hardwario/twr-enclosures/doc/bce202-1.png

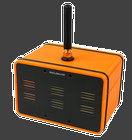
doc/bce202-1.png
