hardwario/twr-enclosures/doc/bce202-2.png

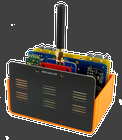
doc/bce202-2.png
