hardwario/twr-enclosures/doc/bce204-1.png

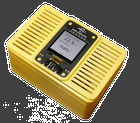
doc/bce204-1.png
