hardwario/twr-enclosures/doc/bce501-1.png

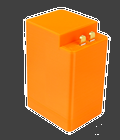
doc/bce501-1.png
