hardwario/twr-enclosures/stl-models/HWE105B.stl

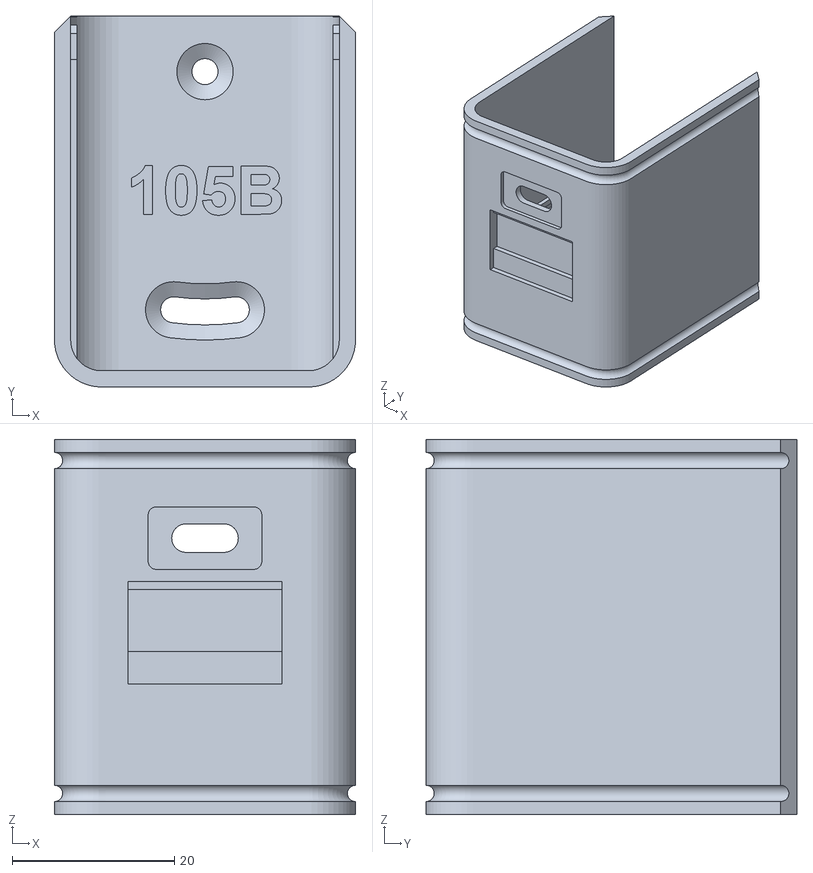
[picture p47: CAD file, 2020-03-29]
stl-models/HWE105B.stl
37.1 x 45.7 x 46.2
