hardwario/twr-enclosures/stl-models/HWE501B.stl

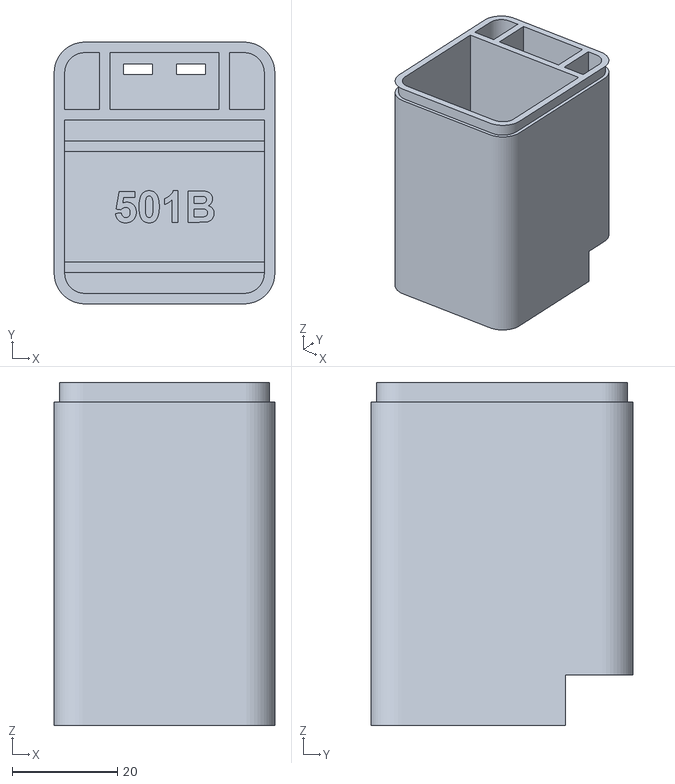
[picture p48: CAD file, 2020-03-29]
stl-models/HWE501B.stl
42.0 x 49.8 x 65.3
