hardwario/twr-enclosures/stl-models/HWE205A.stl

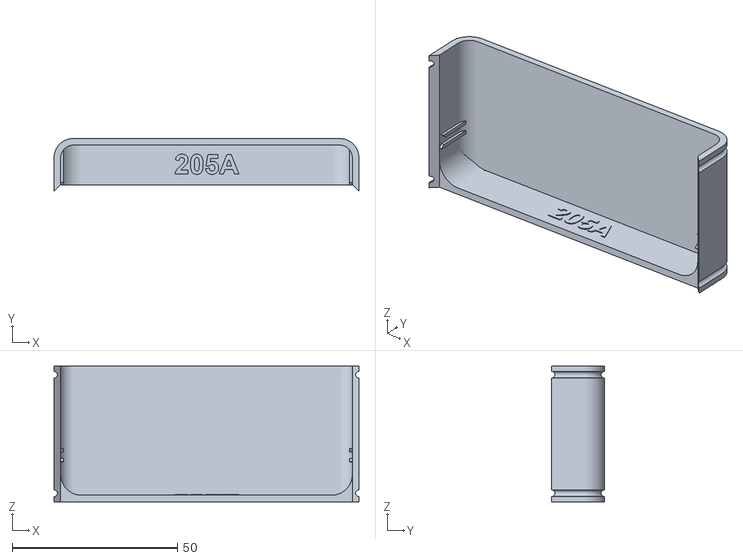
[picture p49: CAD file, 2020-03-29]
stl-models/HWE205A.stl
92.2 x 16.0 x 41.0
