hardwario/twr-enclosures/stl-models/HWE209C.stl

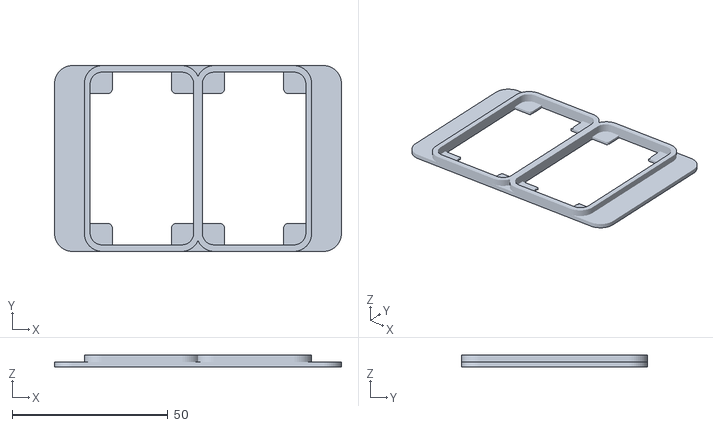
[picture p50: CAD file, 2020-03-29]
stl-models/HWE209C.stl
92.2 x 59.7 x 4.00
