hardwario/twr-enclosures/stl-models/HWE302A.stl

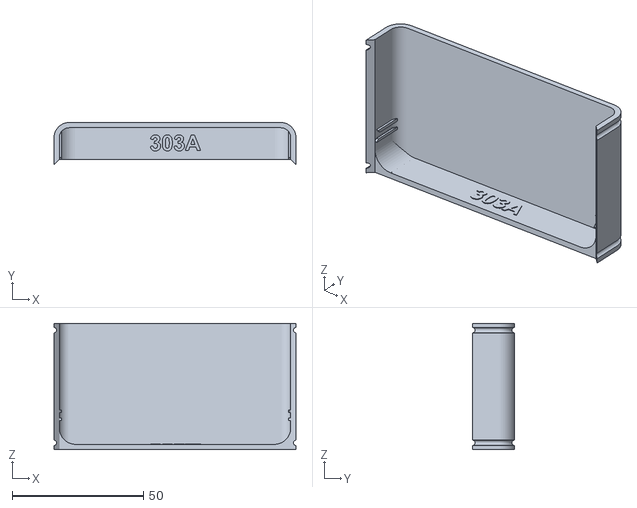
[picture p51: CAD file, 2020-03-29]
stl-models/HWE302A.stl
92.2 x 16.0 x 48.1
