hardwario/twr-enclosures/stl-models/HWE205B.stl

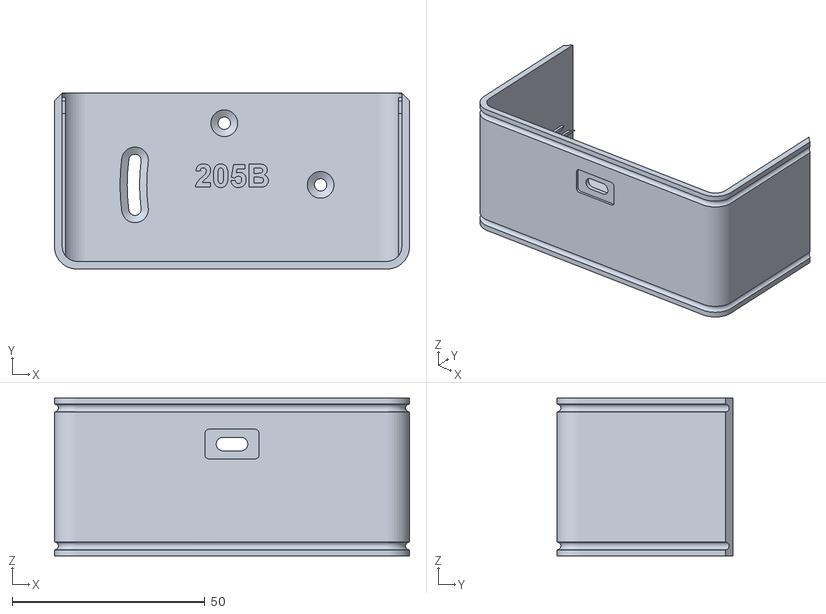
[picture p52: CAD file, 2020-03-29]
stl-models/HWE205B.stl
92.2 x 45.7 x 41.0
