hardwario/twr-enclosures/stl-models/HWE501A.stl

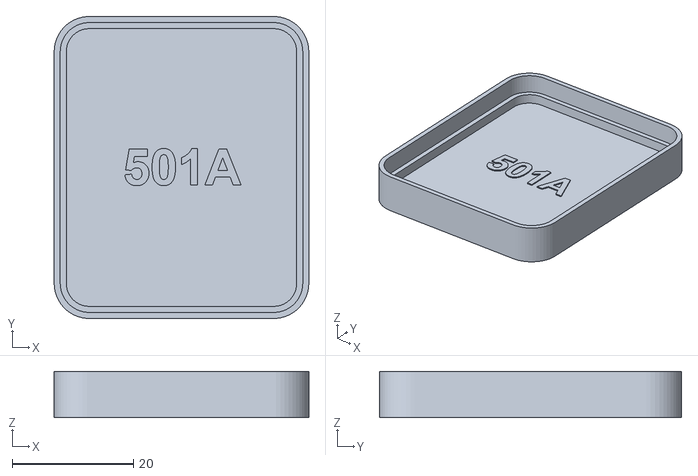
[picture p53: CAD file, 2020-03-29]
stl-models/HWE501A.stl
42.0 x 49.8 x 7.60
