hardwario/twr-enclosures/stl-models/HWE104B.stl

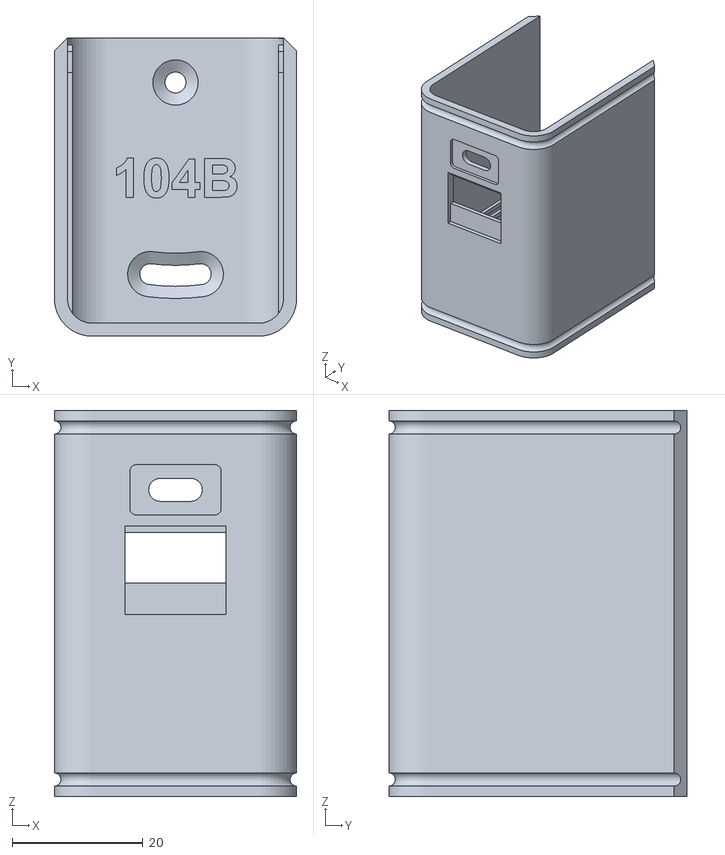
[picture p54: CAD file, 2020-03-29]
stl-models/HWE104B.stl
37.1 x 45.7 x 59.1
