hardwario/twr-enclosures/stl-models/HWE302C.stl

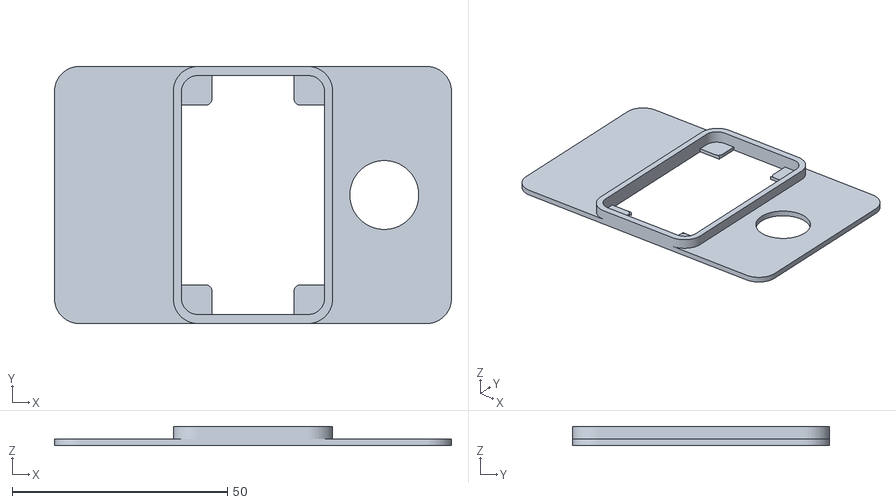
[picture p55: CAD file, 2020-03-29]
stl-models/HWE302C.stl
92.2 x 59.7 x 4.50
