hardwario/twr-enclosures/stl-models/HWE202A.stl

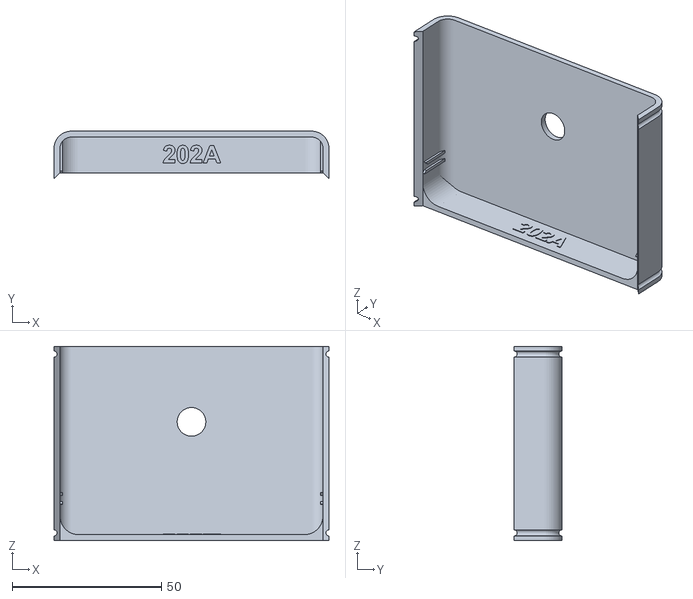
[picture p56: CAD file, 2020-03-29]
stl-models/HWE202A.stl
92.2 x 16.0 x 65.1
