hardwario/twr-enclosures/stl-models/HWE204B.stl

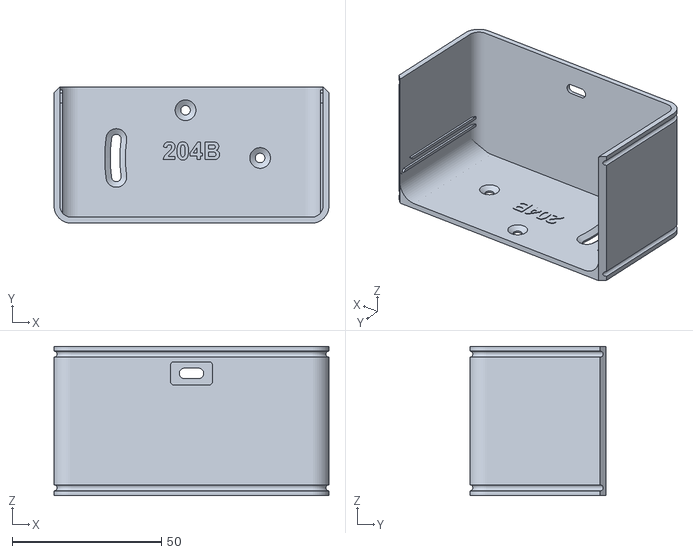
[picture p57: CAD file, 2020-03-29]
stl-models/HWE204B.stl
92.2 x 45.7 x 50.0
