hardwario/twr-enclosures/stl-models/HWE202B.stl

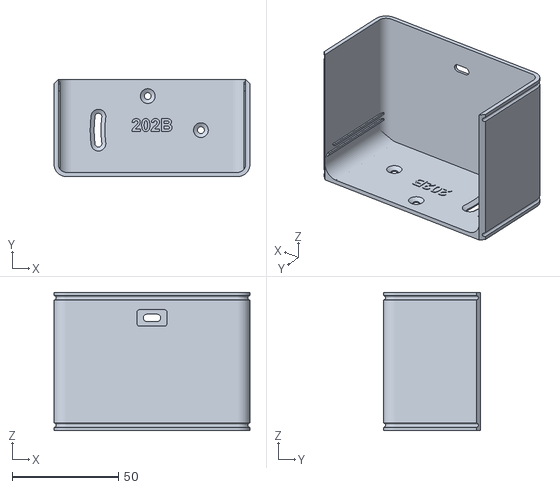
[picture p58: CAD file, 2020-03-29]
stl-models/HWE202B.stl
92.2 x 45.7 x 65.1
