hardwario/twr-enclosures/stl-models/HWE204C.stl

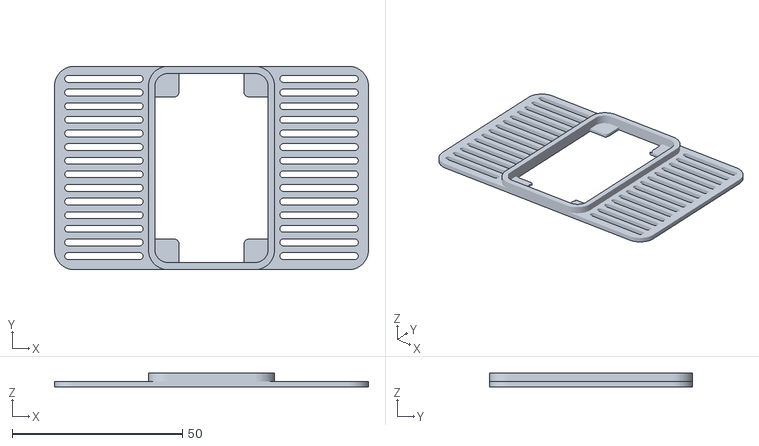
[picture p59: CAD file, 2020-03-29]
stl-models/HWE204C.stl
92.2 x 59.7 x 4.00
