hardwario/twr-enclosures/stl-models/HWE305A.stl

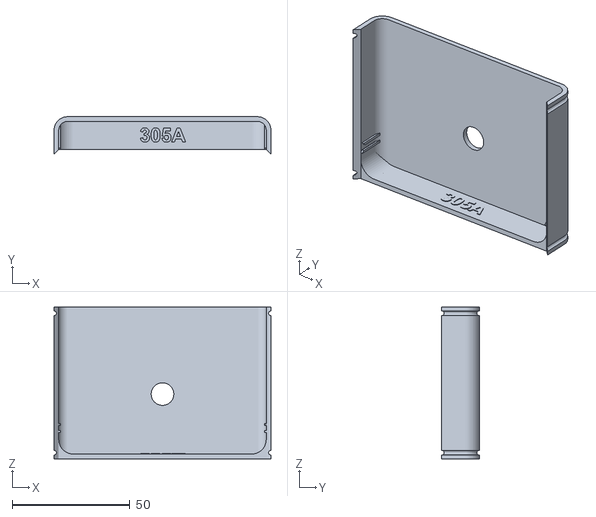
[picture p60: CAD file, 2020-03-29]
stl-models/HWE305A.stl
92.2 x 16.0 x 64.4
