hardwario/twr-enclosures/stl-models/HWE101B.stl

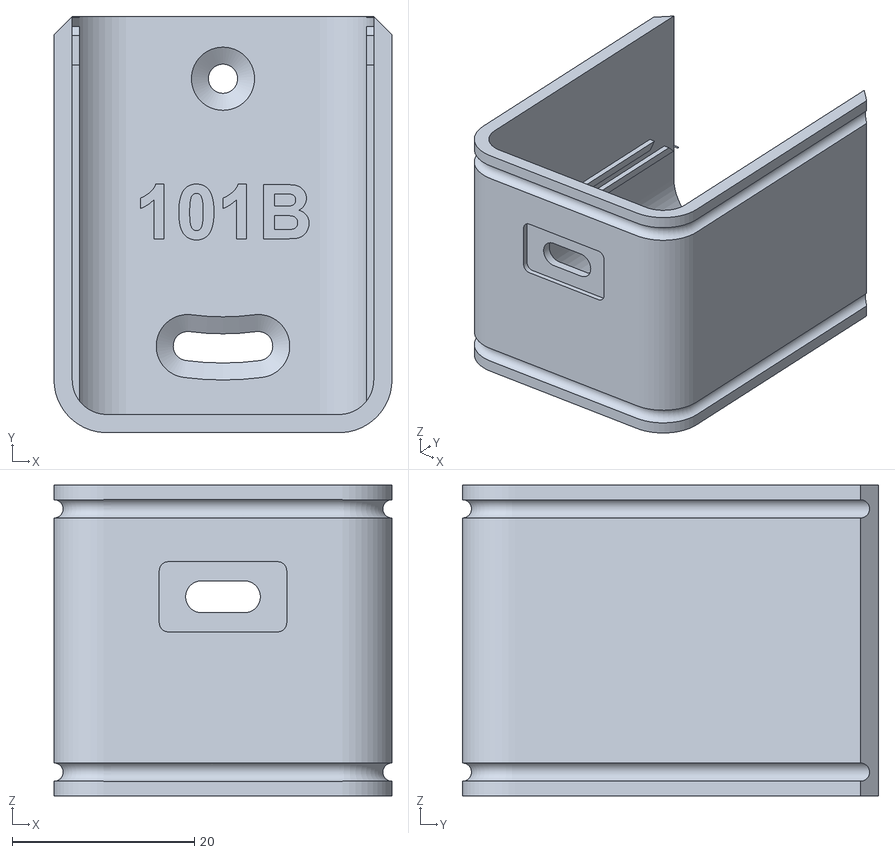
[picture p61: CAD file, 2020-03-29]
stl-models/HWE101B.stl
37.1 x 45.7 x 34.1
