hardwario/twr-enclosures/stl-models/HWE206A.stl

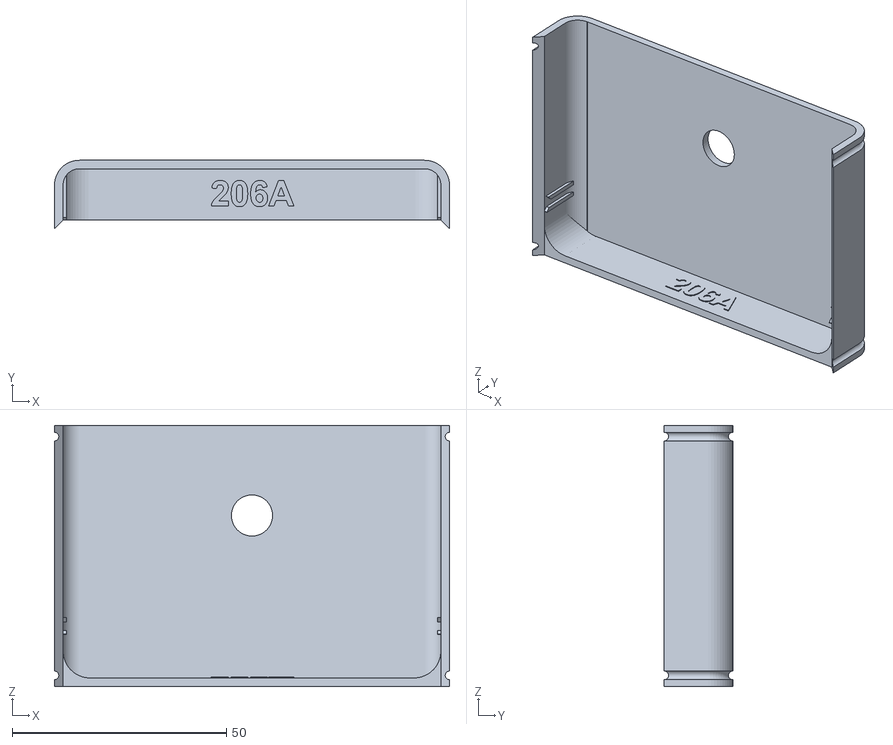
[picture p62: CAD file, 2020-03-29]
stl-models/HWE206A.stl
92.2 x 16.0 x 60.9
