hardwario/twr-enclosures/stl-models/HWE203B.stl

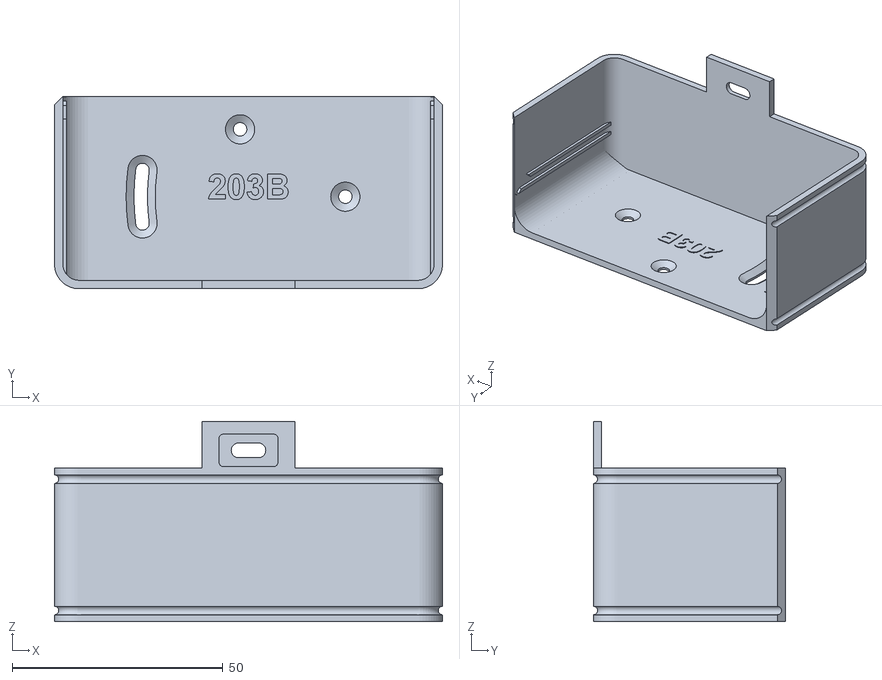
[picture p63: CAD file, 2020-03-29]
stl-models/HWE203B.stl
92.2 x 45.7 x 47.5
