hardwario/twr-enclosures/stl-models/HWE302B.stl

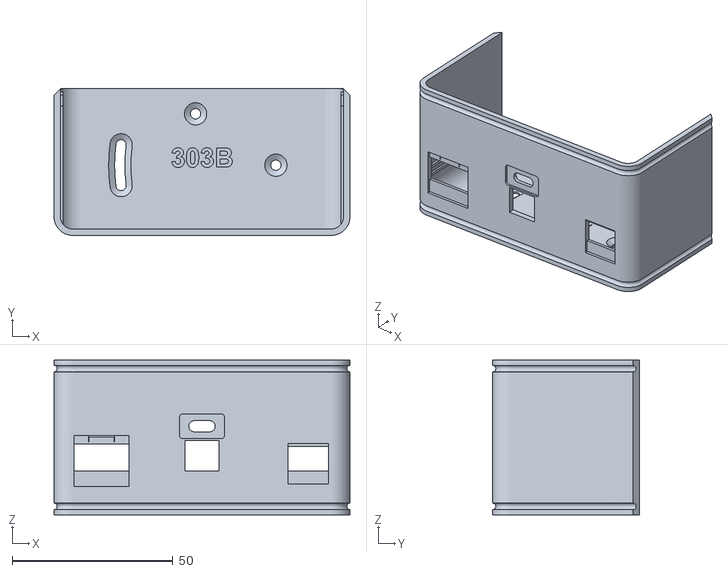
[picture p64: CAD file, 2020-03-29]
stl-models/HWE302B.stl
92.2 x 45.7 x 48.1
