hardwario/twr-enclosures/stl-models/HWE401A.stl

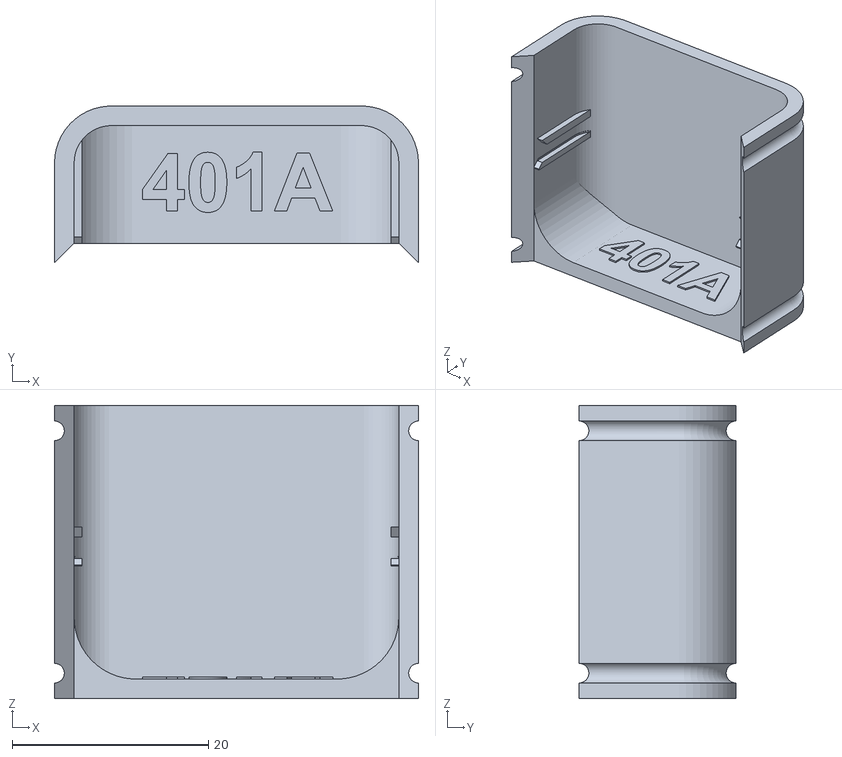
[picture p65: CAD file, 2020-03-29]
stl-models/HWE401A.stl
37.1 x 16.0 x 29.9
