hardwario/twr-enclosures/stl-models/HWE103A.stl

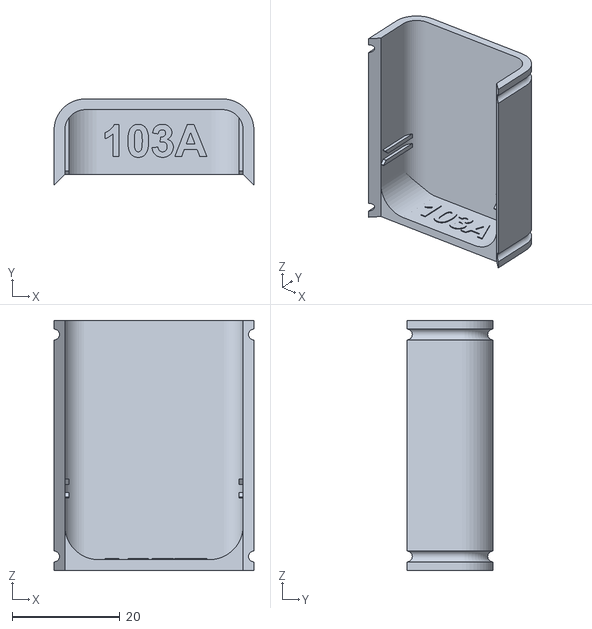
[picture p66: CAD file, 2020-03-29]
stl-models/HWE103A.stl
37.1 x 16.0 x 46.4
