hardwario/twr-enclosures/stl-models/HWE402B.stl

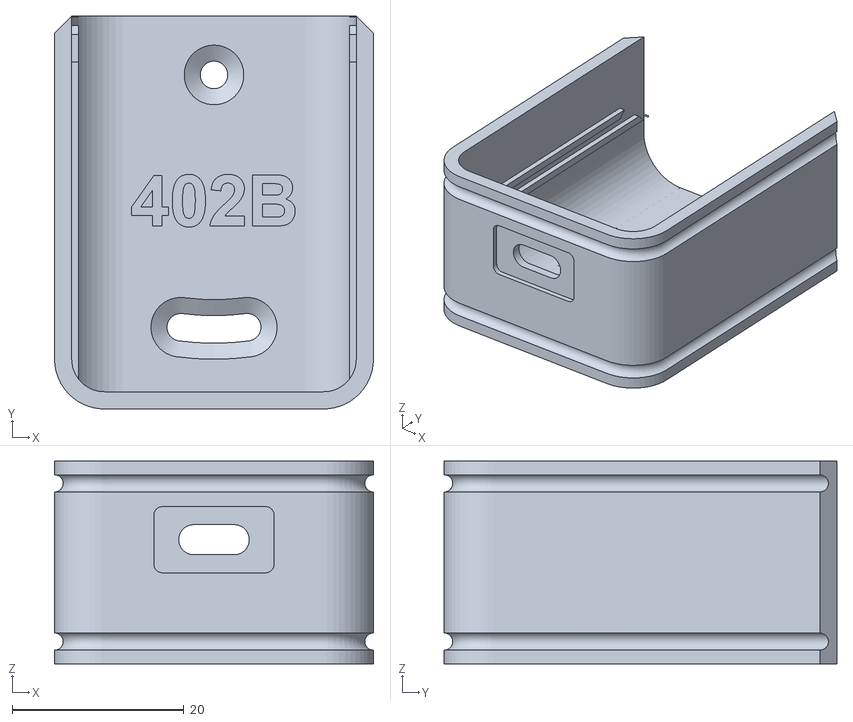
[picture p67: CAD file, 2020-03-29]
stl-models/HWE402B.stl
37.1 x 45.7 x 23.6
