hardwario/twr-enclosures/stl-models/HWE203A.stl

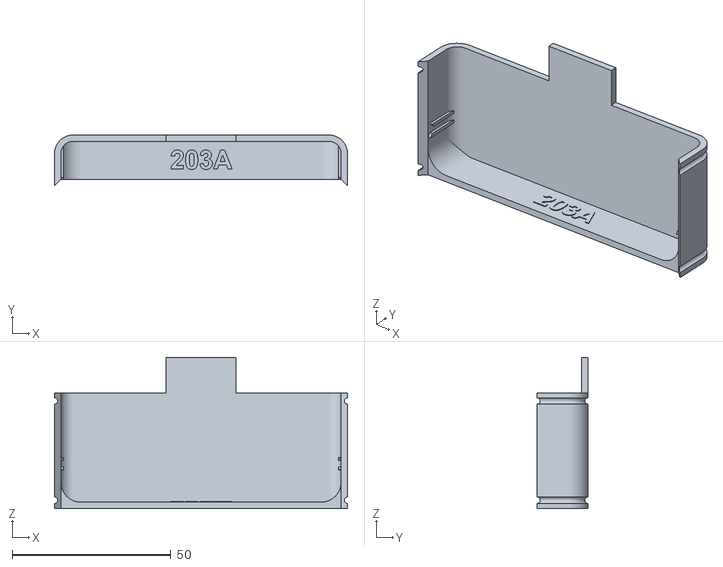
[picture p68: CAD file, 2020-03-29]
stl-models/HWE203A.stl
92.2 x 16.0 x 47.5
