hardwario/twr-enclosures/stl-models/HWE401B.stl

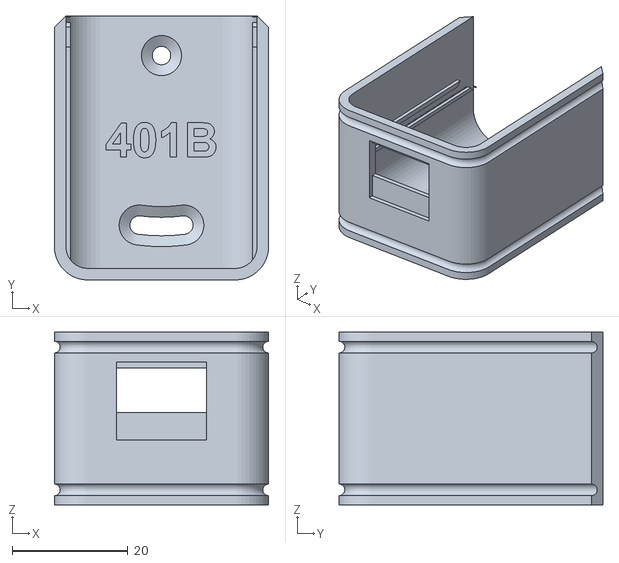
[picture p69: CAD file, 2020-03-29]
stl-models/HWE401B.stl
37.1 x 45.7 x 29.9
