hardwario/twr-enclosures/stl-models/HWE502A.stl

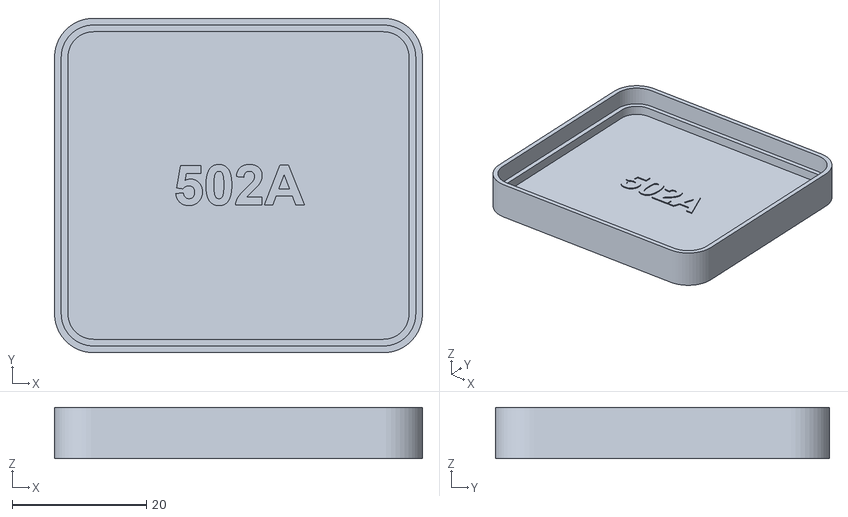
[picture p70: CAD file, 2020-03-29]
stl-models/HWE502A.stl
54.8 x 49.8 x 7.60
