hardwario/twr-enclosures/stl-models/HWE109A.stl

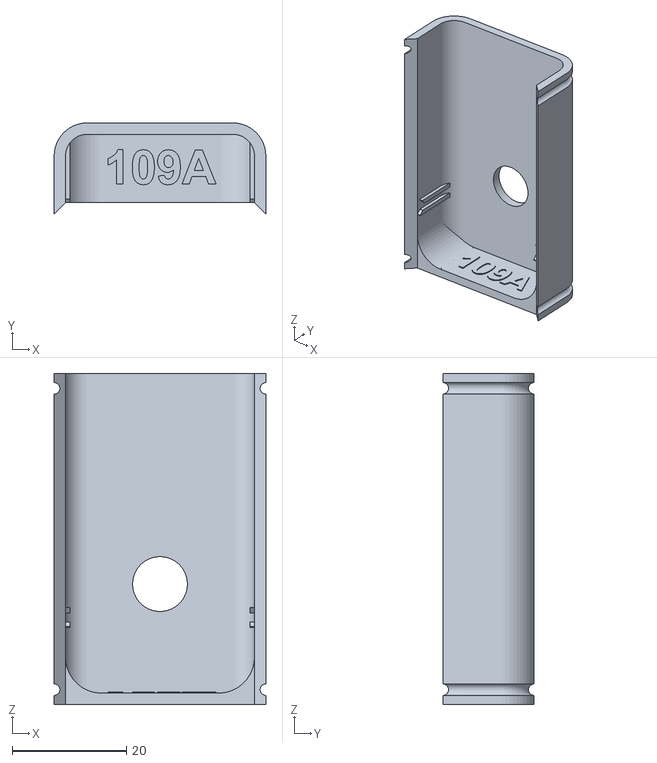
[picture p71: CAD file, 2020-03-29]
stl-models/HWE109A.stl
37.1 x 16.0 x 58.0
