hardwario/twr-enclosures/stl-models/HWE305B.stl

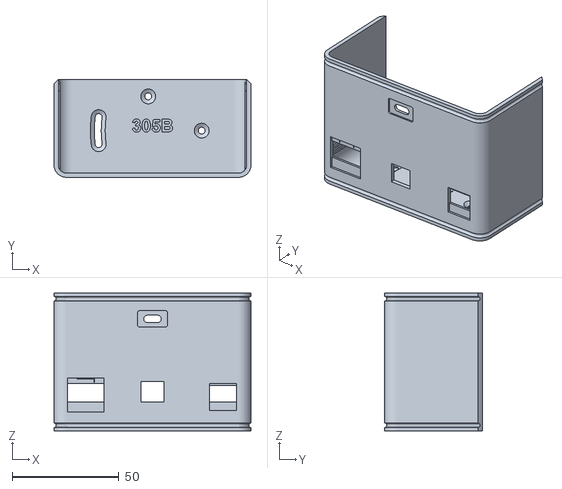
[picture p72: CAD file, 2020-03-29]
stl-models/HWE305B.stl
92.2 x 45.7 x 64.4
