hardwario/twr-enclosures/stl-models/HWE204A.stl

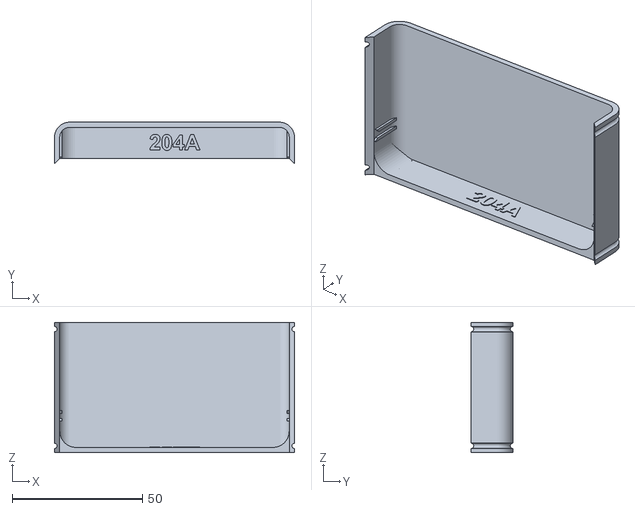
[picture p73: CAD file, 2020-03-29]
stl-models/HWE204A.stl
92.2 x 16.0 x 50.0
