hardwario/twr-enclosures/stl-models/HWE402A.stl

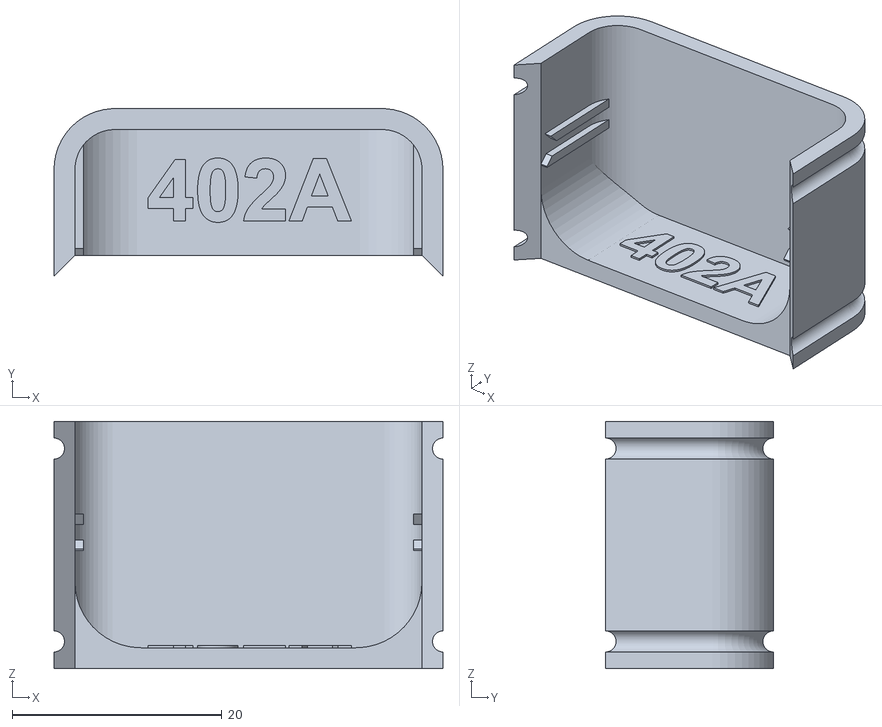
[picture p74: CAD file, 2020-03-29]
stl-models/HWE402A.stl
37.1 x 16.0 x 23.6
