hardwario/twr-enclosures/stl-models/HWE301B.stl

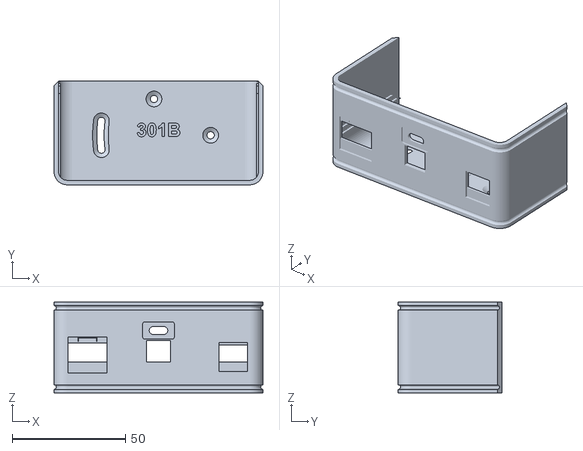
[picture p75: CAD file, 2020-03-29]
stl-models/HWE301B.stl
92.2 x 45.7 x 40.1
