hardwario/twr-enclosures/stl-models/bce201b-r1.stl

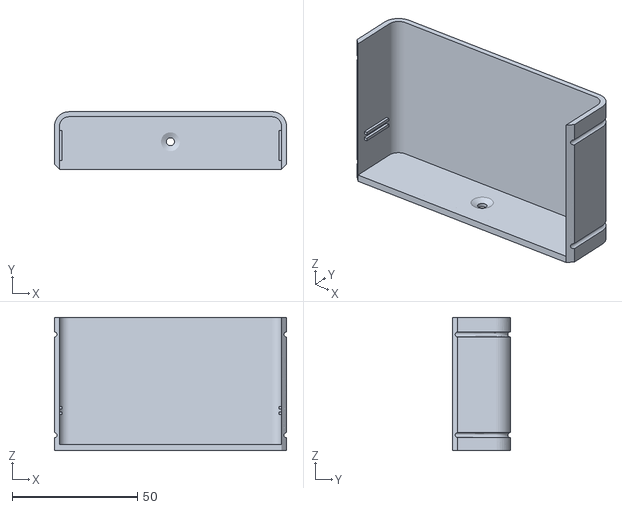
[picture p76: CAD file, 2018-06-28]
stl-models/bce201b-r1.stl
92.6 x 23.0 x 53.2
