hardwario/twr-enclosures/stl-models/bce201a-r1.stl

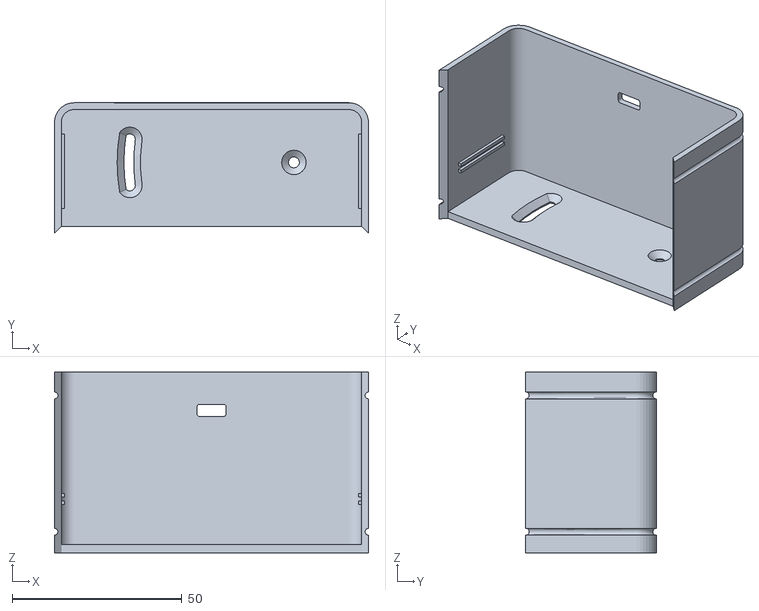
[picture p77: CAD file, 2018-06-28]
stl-models/bce201a-r1.stl
92.6 x 38.5 x 53.3
