hardwario/twr-enclosures/stl-models/bce101b-r2.stl

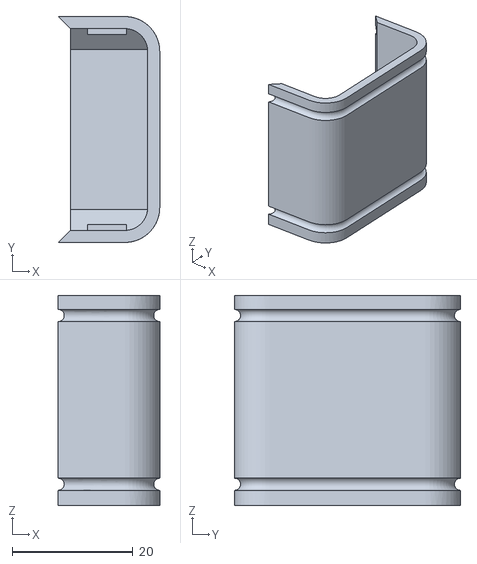
[picture p78: CAD file, 2018-06-28]
stl-models/bce101b-r2.stl
16.9 x 37.5 x 34.9
