hardwario/twr-enclosures/stl-models/bce101a-r2.stl

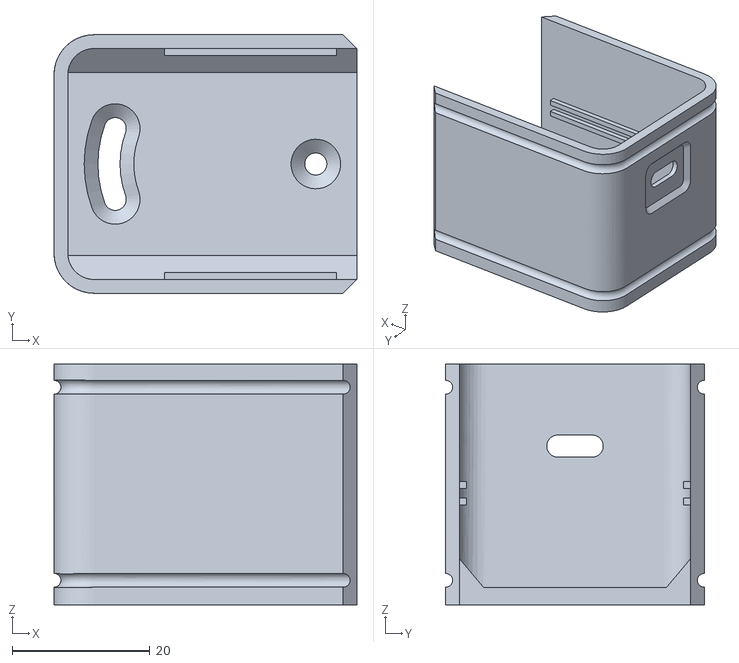
[picture p79: CAD file, 2018-06-28]
stl-models/bce101a-r2.stl
44.0 x 37.5 x 34.9
