hardwario/twr-enclosures/stl-models/bce301a-r1.stl

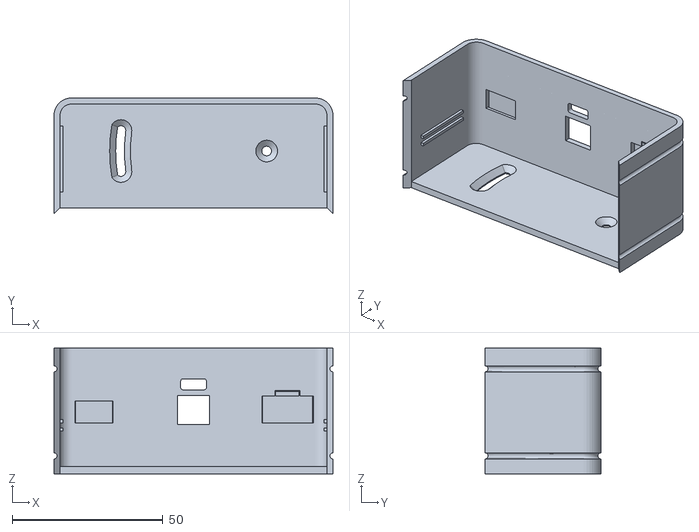
[picture p80: CAD file, 2018-04-12]
stl-models/bce301a-r1.stl
92.6 x 38.5 x 41.8
