hardwario/twr-enclosures/stl-models/bce204c-r1.stl

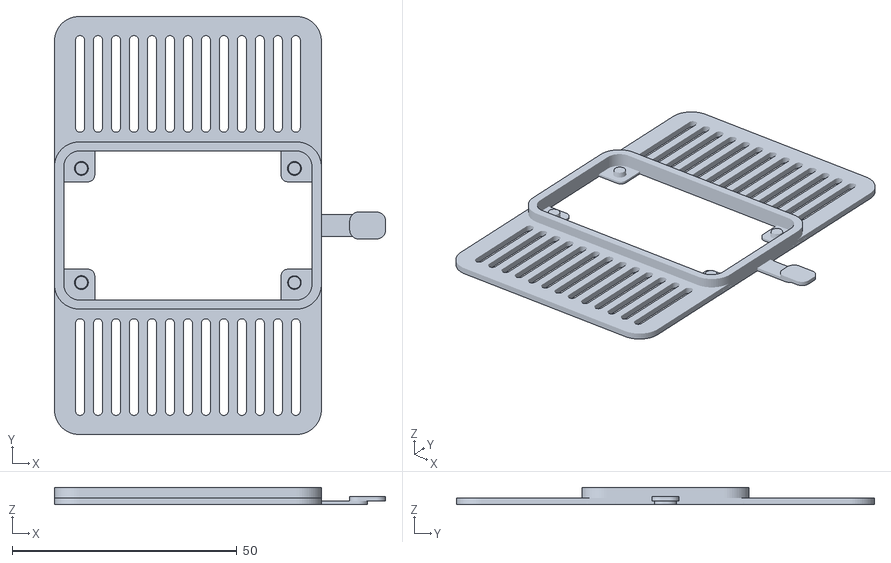
[picture p81: CAD file, 2018-04-12]
stl-models/bce204c-r1.stl
73.7 x 93.0 x 3.80
