hardwario/twr-enclosures/stl-models/pir-sc-r1.stl

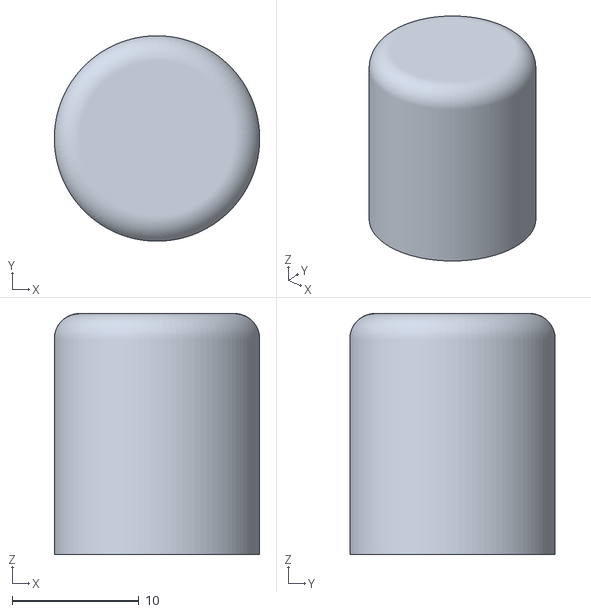
[picture p82: CAD file, 2018-04-12]
stl-models/pir-sc-r1.stl
16.2 x 16.2 x 19.0
