hardwario/twr-enclosures/stl-models/bce204a-r1.stl

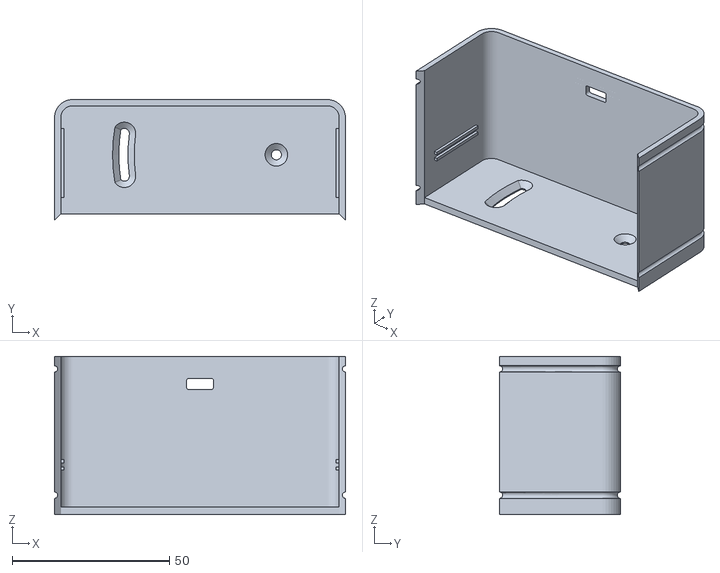
[picture p83: CAD file, 2018-04-12]
stl-models/bce204a-r1.stl
92.6 x 38.5 x 50.4
