hardwario/twr-enclosures/stl-models/bce204b-r1.stl

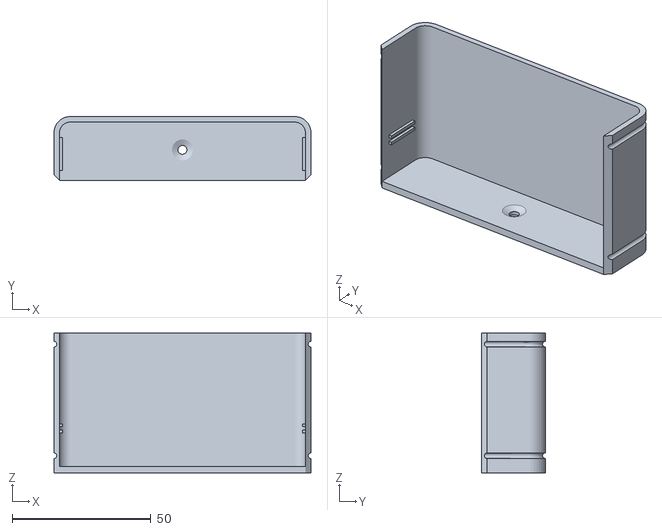
[picture p84: CAD file, 2018-04-12]
stl-models/bce204b-r1.stl
92.6 x 23.0 x 50.4
