hardwario/twr-enclosures/stl-models/bce301b-r1.stl

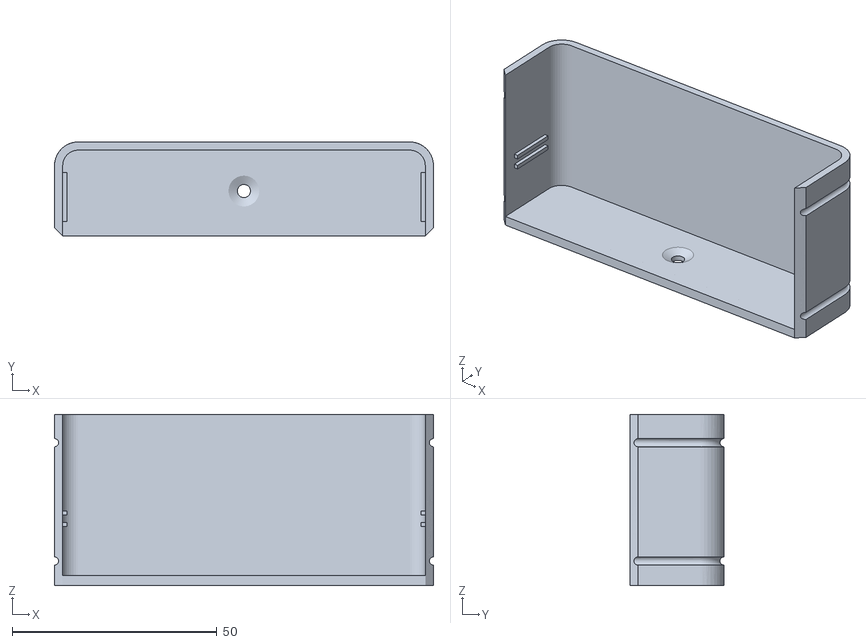
[picture p85: CAD file, 2018-04-12]
stl-models/bce301b-r1.stl
92.6 x 23.0 x 41.8
