hardwario/twr-enclosures/stl-models/bce104b-r1.stl

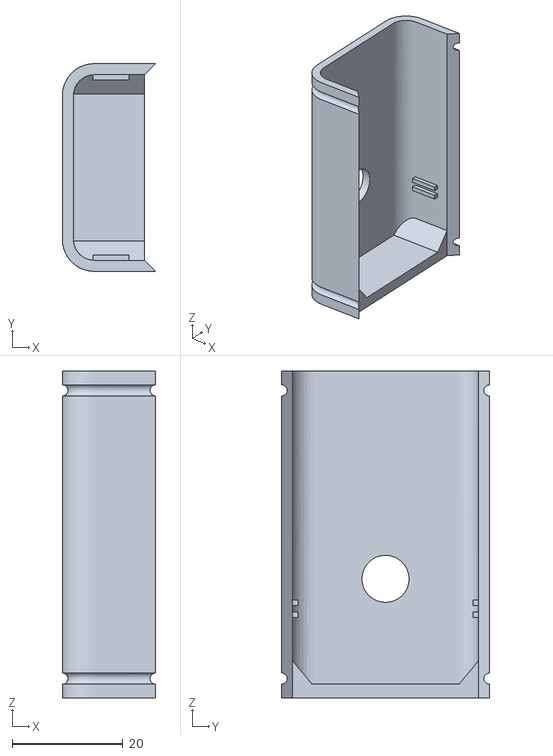
[picture p86: CAD file, 2018-02-11]
stl-models/bce104b-r1.stl
16.9 x 37.5 x 59.0
