hardwario/twr-enclosures/stl-models/bce104a-r1.stl

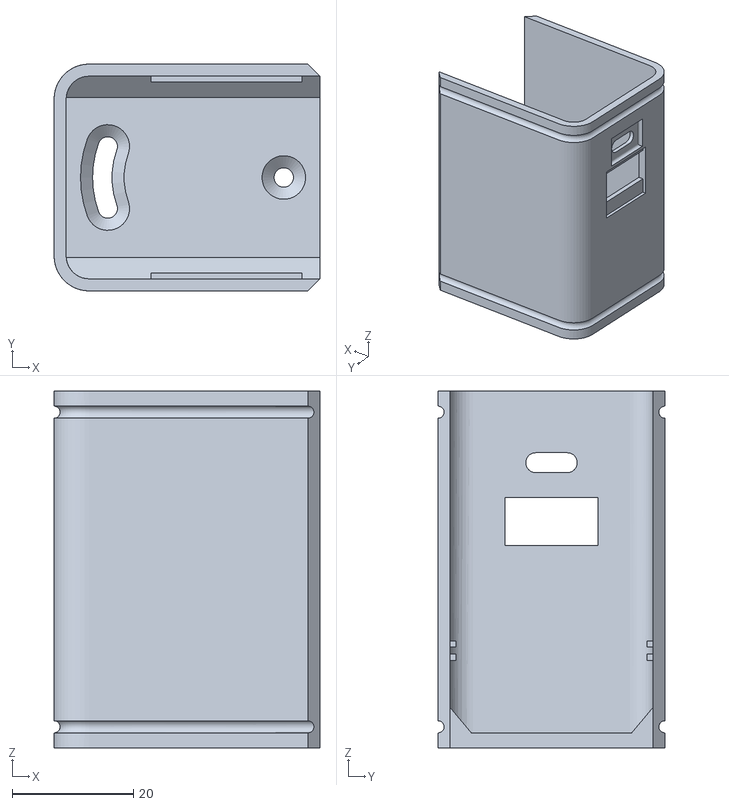
[picture p87: CAD file, 2018-02-11]
stl-models/bce104a-r1.stl
43.9 x 37.5 x 59.0
