hardwario/twr-enclosures/stl-models/pir-cv-r1.stl

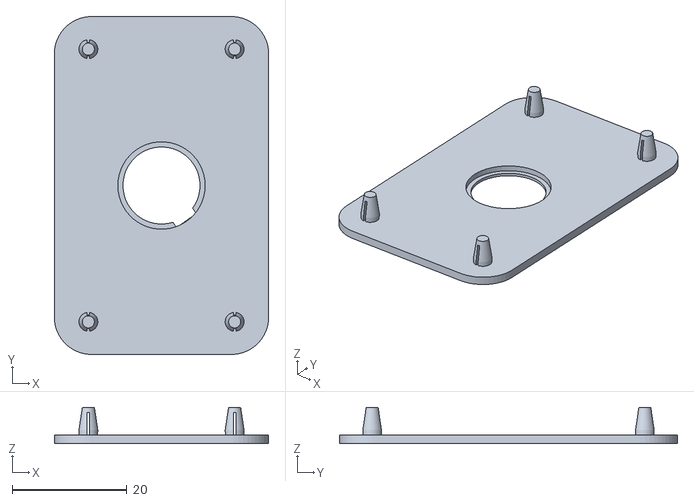
[picture p88: CAD file, 2018-02-03]
stl-models/pir-cv-r1.stl
37.3 x 58.8 x 6.30
