hardwario/twr-enclosures/stl-models/led-hd-b-r1.stl

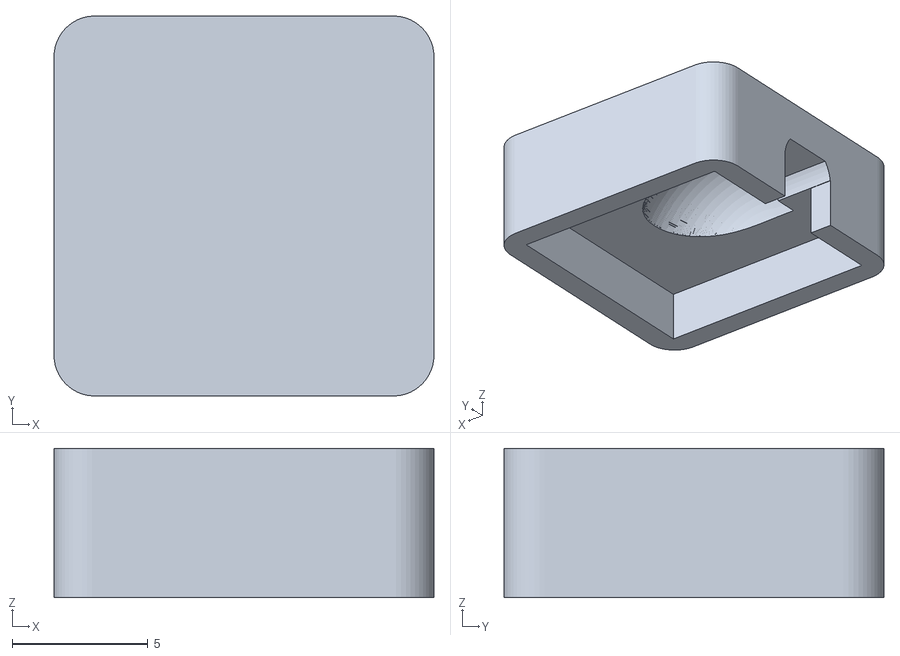
[picture p89: CAD file, 2018-02-03]
stl-models/led-hd-b-r1.stl
14.0 x 14.0 x 5.50
