hardwario/twr-enclosures/stl-models/led-hd-a-r1.stl

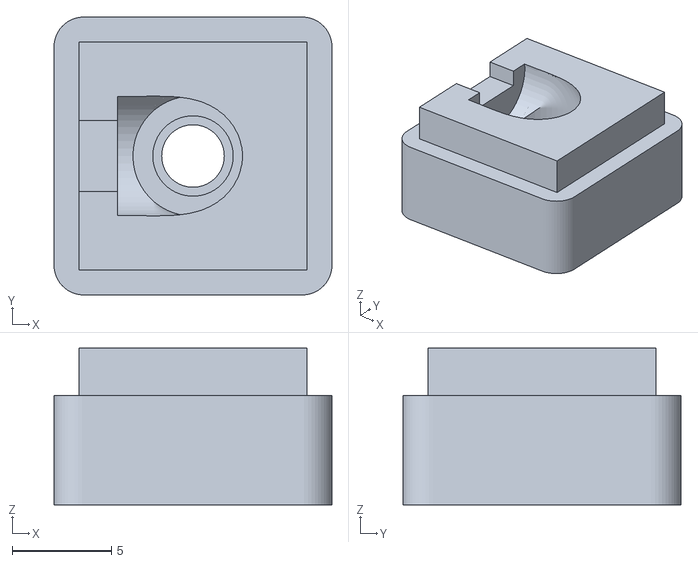
[picture p90: CAD file, 2018-02-03]
stl-models/led-hd-a-r1.stl
14.0 x 14.0 x 7.90
