hardwario/twr-enclosures/stl-models/bce101b-r1.stl

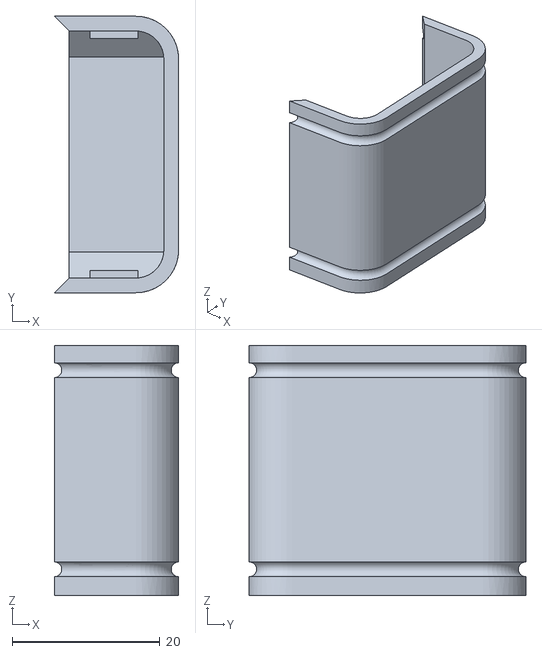
[picture p91: CAD file, 2018-02-03]
stl-models/bce101b-r1.stl
16.8 x 37.5 x 33.9
