hardwario/twr-enclosures/stl-models/bce101a-r1.stl

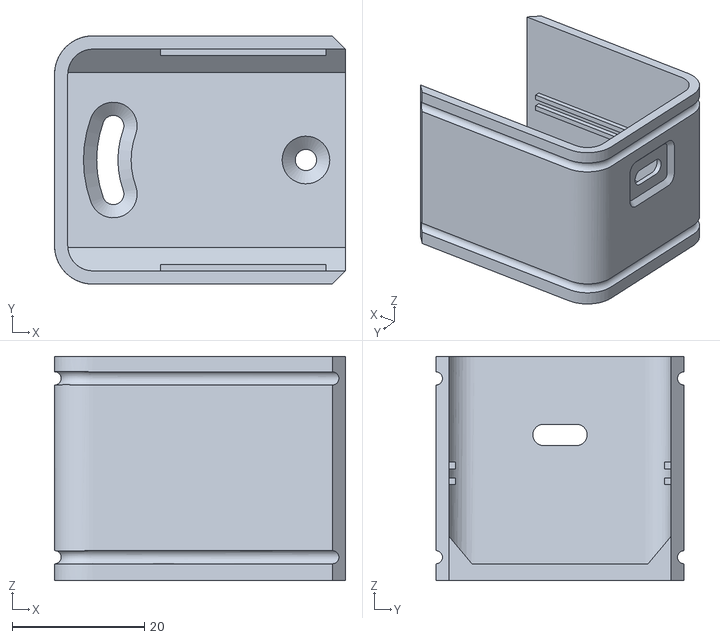
[picture p92: CAD file, 2018-02-03]
stl-models/bce101a-r1.stl
44.0 x 37.5 x 33.9
