hardwario/twr-enclosures/stl-models/bce203c-r1.stl

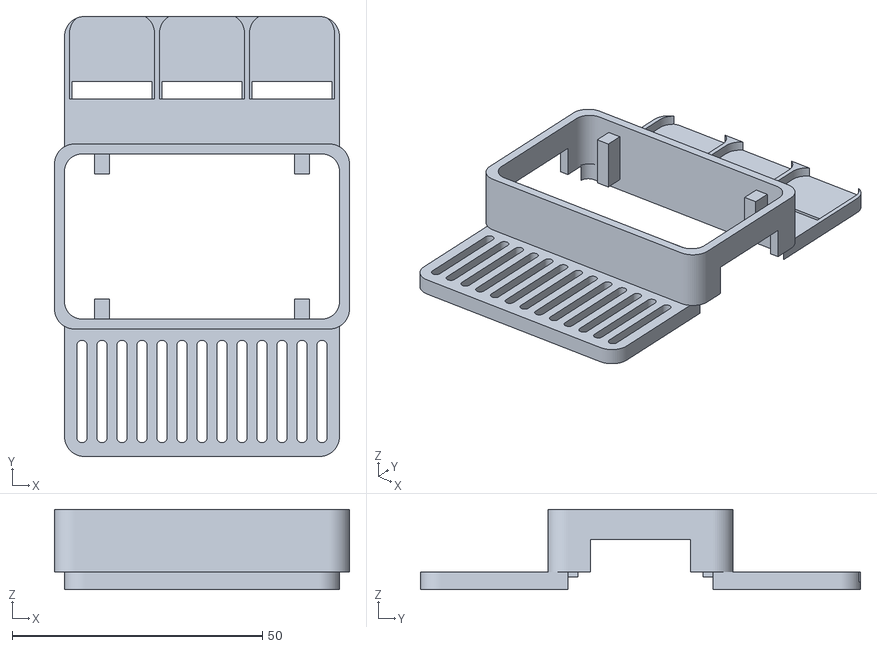
[picture p93: CAD file, 2018-02-03]
stl-models/bce203c-r1.stl
59.0 x 88.0 x 16.0
