hardwario/twr-enclosures/stl-models/bce203b-r1.stl

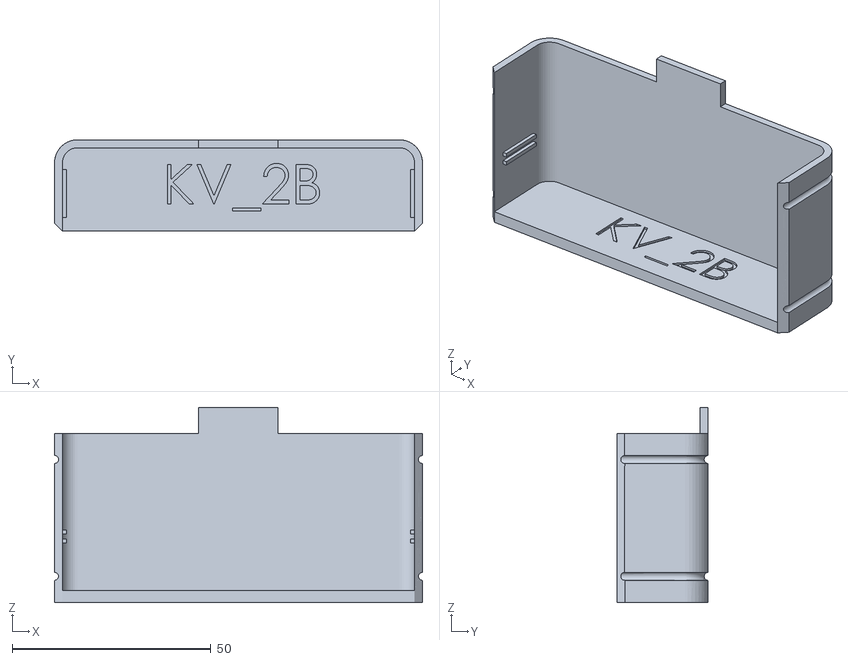
[picture p94: CAD file, 2018-02-03]
stl-models/bce203b-r1.stl
92.6 x 23.0 x 49.1
