hardwario/twr-enclosures/stl-models/bce103b-r1.stl

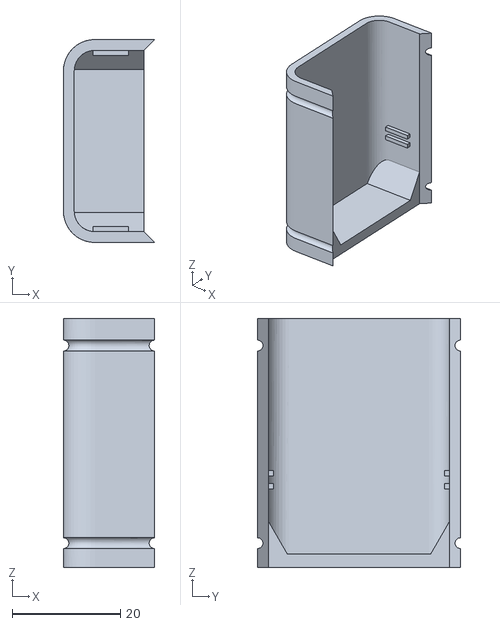
[picture p95: CAD file, 2018-02-03]
stl-models/bce103b-r1.stl
16.9 x 37.5 x 46.0
