hardwario/twr-enclosures/stl-models/bce103a-r1.stl

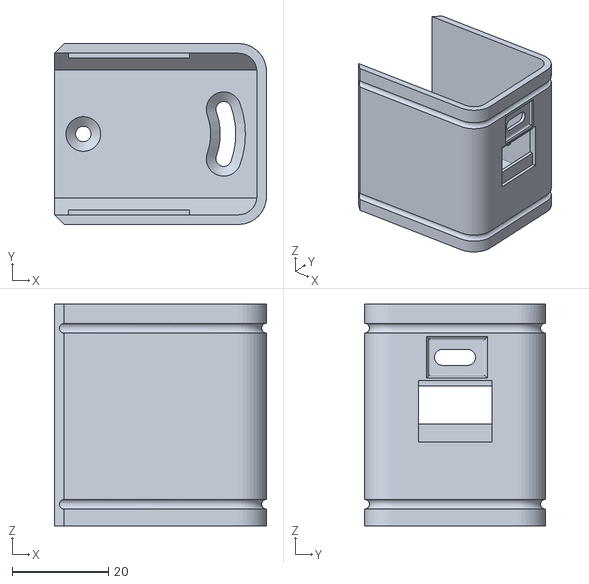
[picture p96: CAD file, 2018-02-03]
stl-models/bce103a-r1.stl
44.0 x 37.5 x 46.0
