hardwario/twr-enclosures/stl-models/bce203a-r1.stl

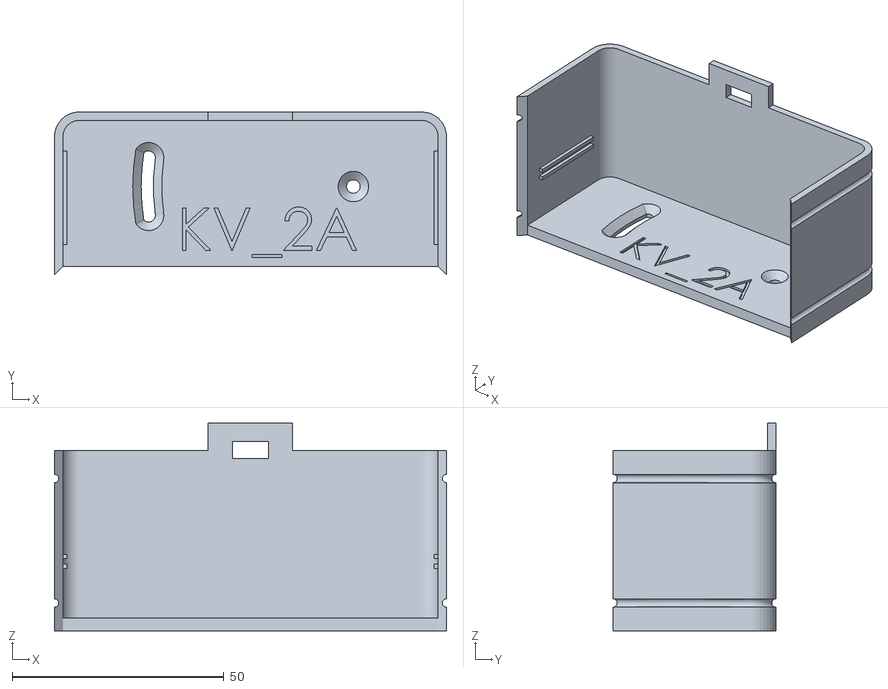
[picture p97: CAD file, 2018-02-03]
stl-models/bce203a-r1.stl
92.6 x 38.5 x 49.1
