hardwario/twr-enclosures/stl-models/bce303a-r1.stl

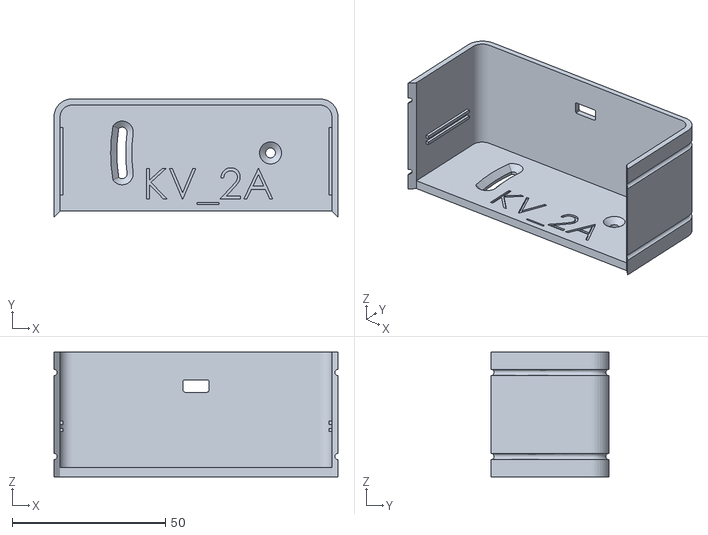
[picture p98: CAD file, 2018-01-15]
stl-models/bce303a-r1.stl
92.6 x 38.5 x 40.6
