hardwario/twr-enclosures/stl-models/bce501b-r1.stl

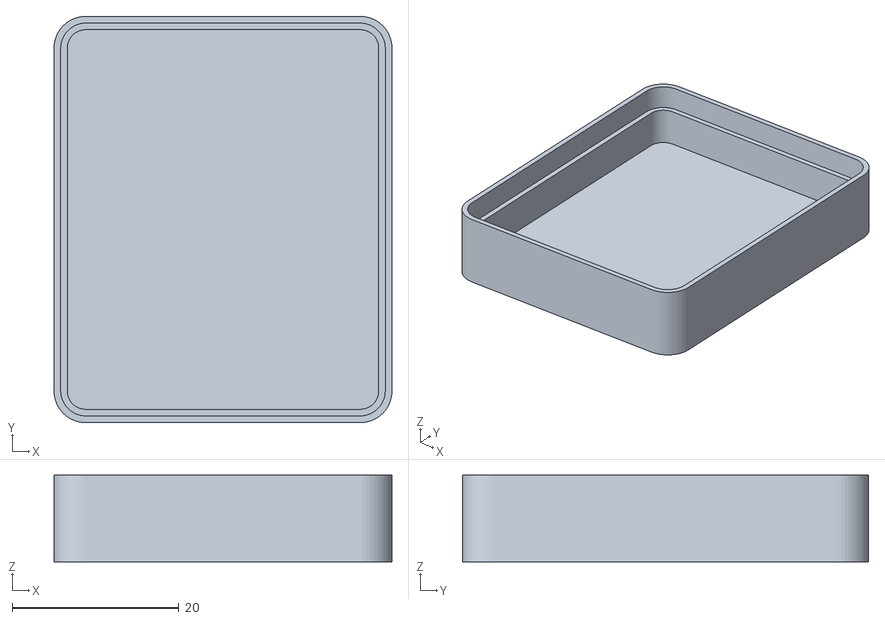
[picture p99: CAD file, 2017-10-17]
stl-models/bce501b-r1.stl
40.6 x 48.8 x 10.5
