hardwario/twr-enclosures/stl-models/bce501a-r1.stl

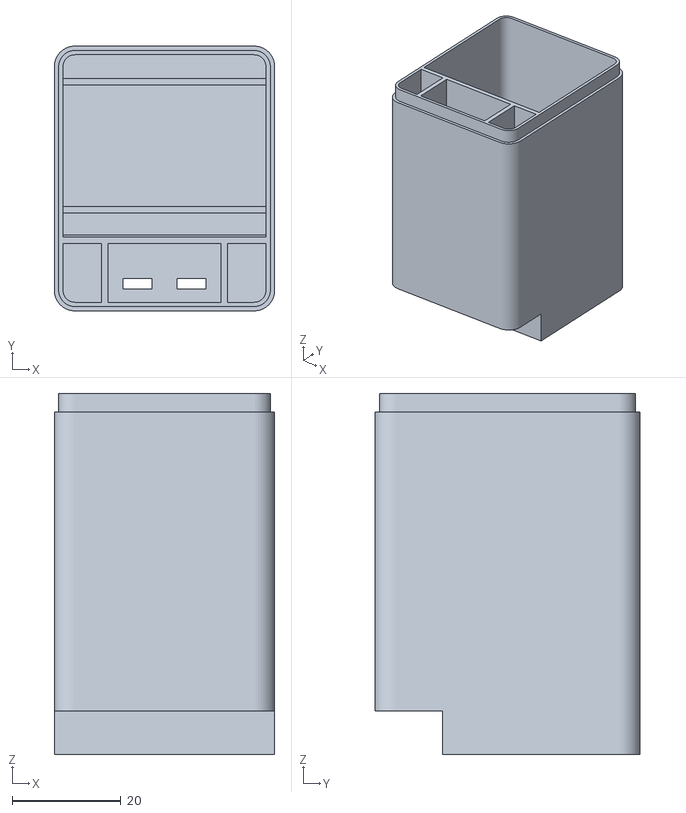
[picture p100: CAD file, 2017-10-17]
stl-models/bce501a-r1.stl
40.6 x 48.8 x 66.5
