hardwario/twr-enclosures/stl-models/bce202b-r1.stl

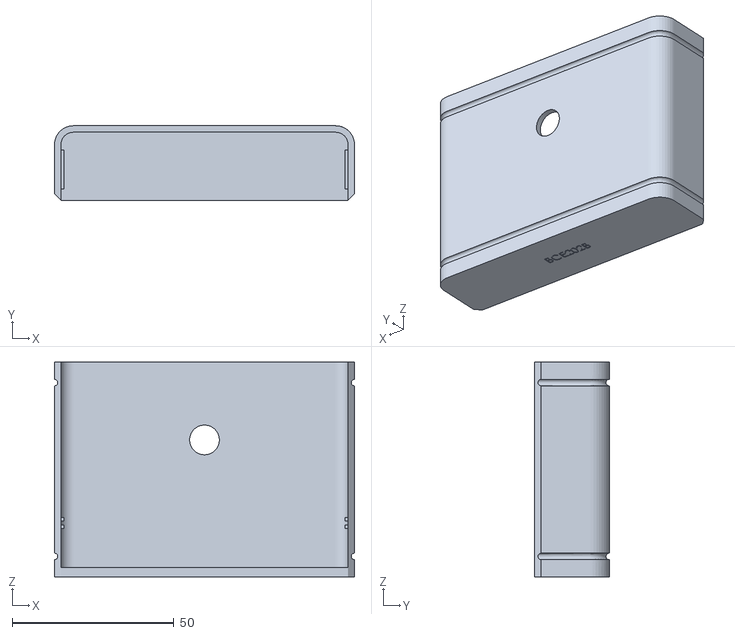
[picture p101: CAD file, 2017-10-01]
stl-models/bce202b-r1.stl
92.6 x 23.0 x 66.3
