hardwario/twr-enclosures/stl-models/bce202a-r1.stl

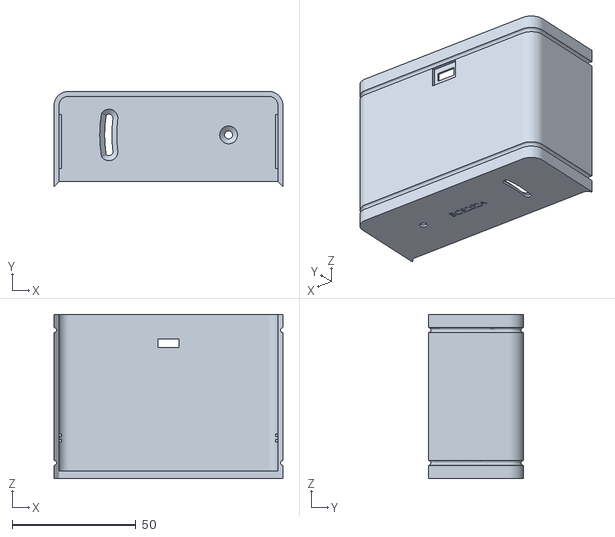
[picture p102: CAD file, 2017-10-01]
stl-models/bce202a-r1.stl
92.6 x 38.5 x 66.3
