hardwario/twr-enclosures/stl-models/bce303b-r1.stl

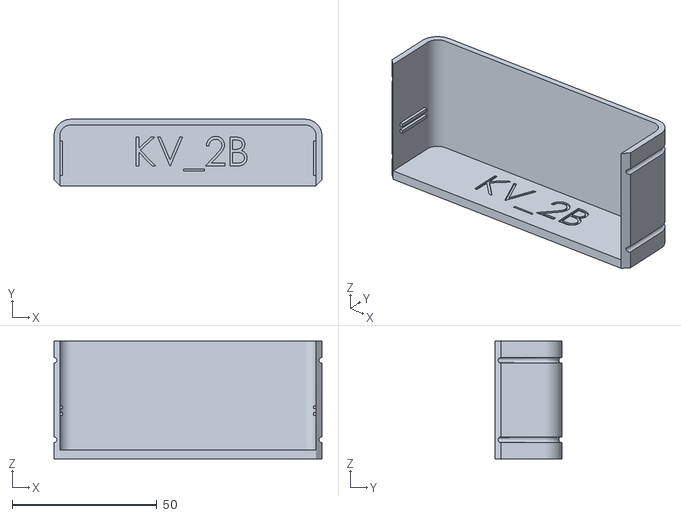
[picture p103: CAD file, 2017-09-14]
stl-models/bce303b-r1.stl
92.6 x 23.0 x 40.6
