hardwario/twr-enclosures/stl-models/bce102b-r1.stl

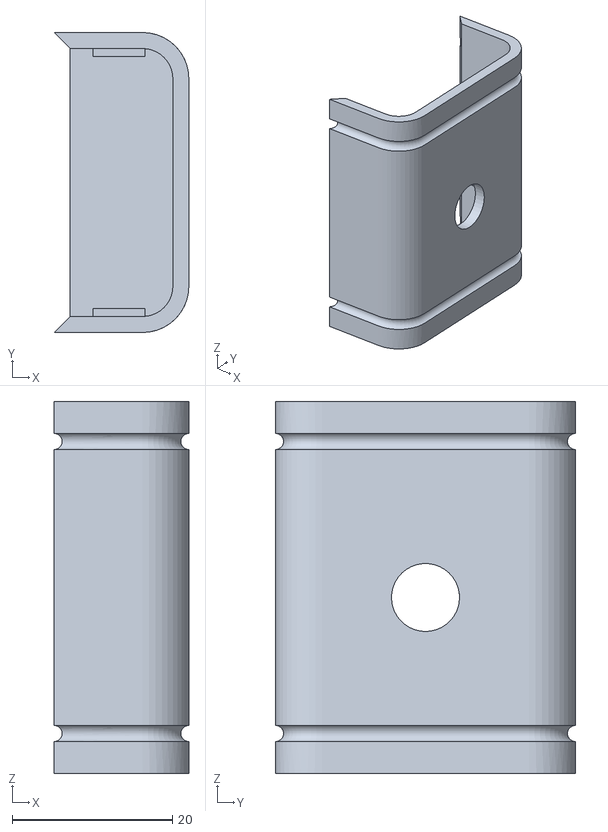
[picture p104: CAD file, 2017-09-14]
stl-models/bce102b-r1.stl
16.9 x 37.5 x 46.5
